dimaib/UBD/schematic_pcb/UBD/cad_Плата отдельно/01.png

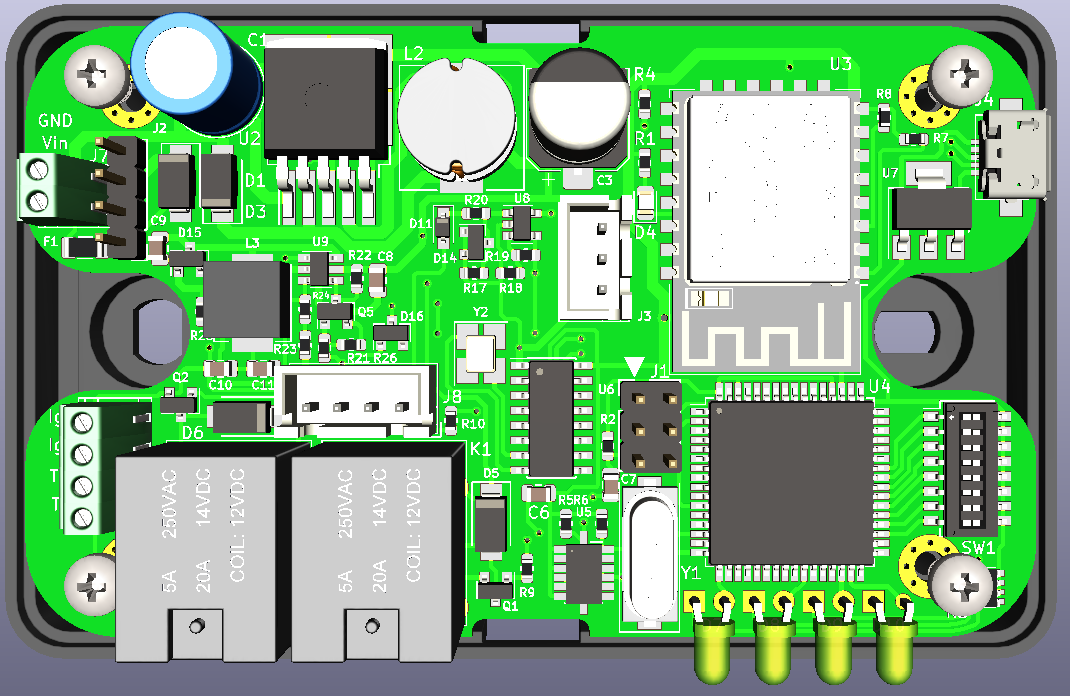
schematic_pcb/UBD/cad_Плата отдельно/01.png
