dimaib/UBD/schematic_pcb/UBD/cad_Плата отдельно/02.png

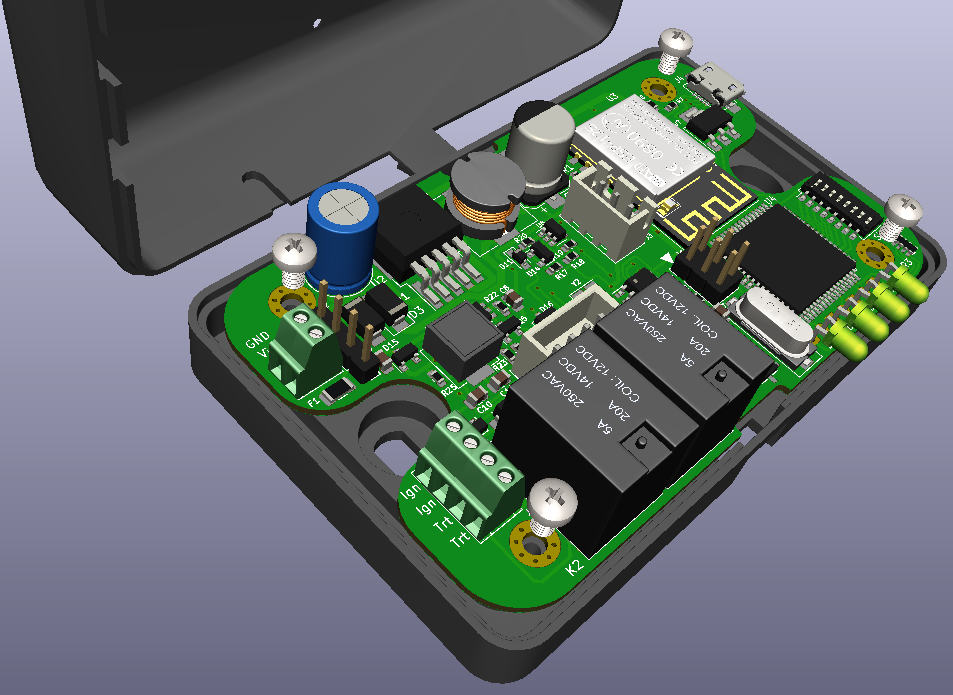
schematic_pcb/UBD/cad_Плата отдельно/02.png
