dimaib/UBD/schematic_pcb/UBD/cad_Плата отдельно/03.png

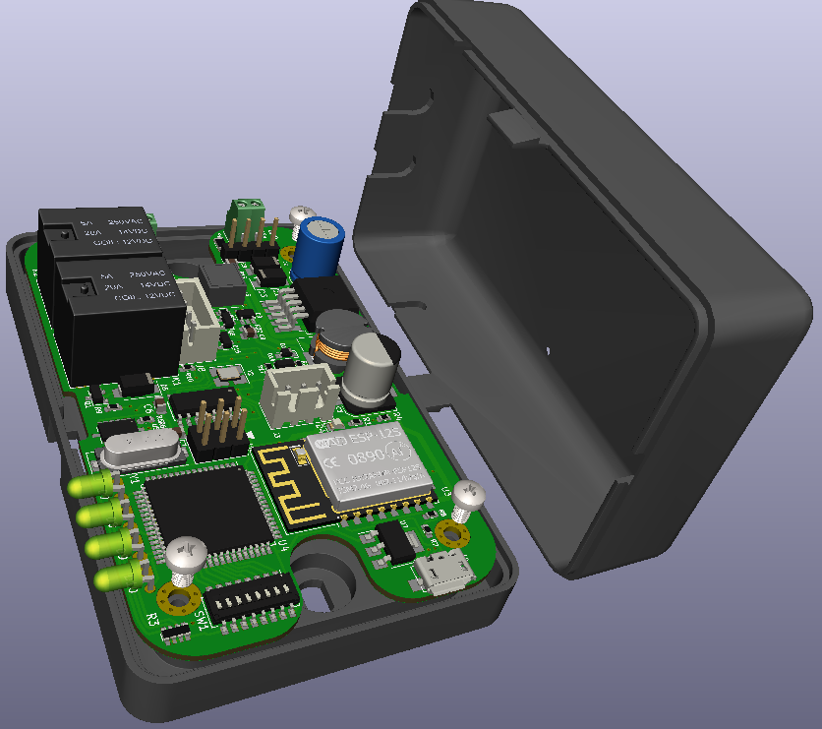
schematic_pcb/UBD/cad_Плата отдельно/03.png
