dimaib/UBD/RFID_USB_carta/Спецификация.xlsx

№ | Наименование | Кол-во | Ном. номер Чип-Дип | Цена за единицу [руб.] | Цена сумма [руб.] | Ссылка
1 | ATmega8A, Микроконтроллер | 1 | 9110051050 | 65.00р. | 65.00р. | https://www.chipdip.ru/product/atmega8a-au
2 | 0.063Вт 0603 68 Ом, 1% | 2 | 9000079612 | 0.90р. | 1.80р. | https://www.chipdip.ru/product0/9000079612
3 | 0.063Вт 0603 1.5 кОм, 1% | 1 | 9000079716 | 0.90р. | 0.90р. | https://www.chipdip.ru/product0/9000079716
4 | Кер.ЧИП конд. 1 мкФ X7R, 10% | 2 | 768017701 | 3.00р. | 6.00р. | https://www.chipdip.ru/product0/768017701
5 | BZV55C3V6, Стабилитрон 3.6В, 5%, 0.5Вт | 2 | 12030485 | 2.00р. | 4.00р. | https://www.chipdip.ru/product/bzv55c3v6
6 | Кварцевый резонатор 12.000 МГц (усечен.) | 1 | 293540794 | 20.00р. | 20.00р. | https://www.chipdip.ru/product/12mhz-hc-49s
7 | MATRIX- II Cчитыватель proximity-карт | 1 | 8760088881 | 1560.00р. | 1560.00р. | https://www.chipdip.ru/product0/8760088881
8 | KLS1-233-0-0-1-T (Micro USB 5S-B), Разъём | 1 | 9000313769 | 7.00р. | 7.00р. | https://www.chipdip.ru/product/micro-usb-5s-b
9 | PLS-40R (DS1022-1x40R), Вилка штыревая 2.54мм 1х40 угловая (тип D1) | 1 | 11734 | 16.00р. | 16.00р. | https://www.chipdip.ru/product/pls-40r
10 | PLD-6 (DS1021-2x3S), Вилка штыревая 2.54мм 2x3 прямая тип1 | 2 | 612994781 | 3.00р. | 6.00р. | https://www.chipdip.ru/product/pld-6
11 | FR4 50х100мм 35/35 (1.5мм, 35мкм), Cтеклотекстолит 2-сторонний | 1 | 9000269528 | 120.00р. | 120.00р. | https://www.chipdip.ru/product/fr4-50x100mm-2s
 |  |  |  | Итого: | 1806.70р.
